khinds10/EnvironmentClock/display/displayCommands.png

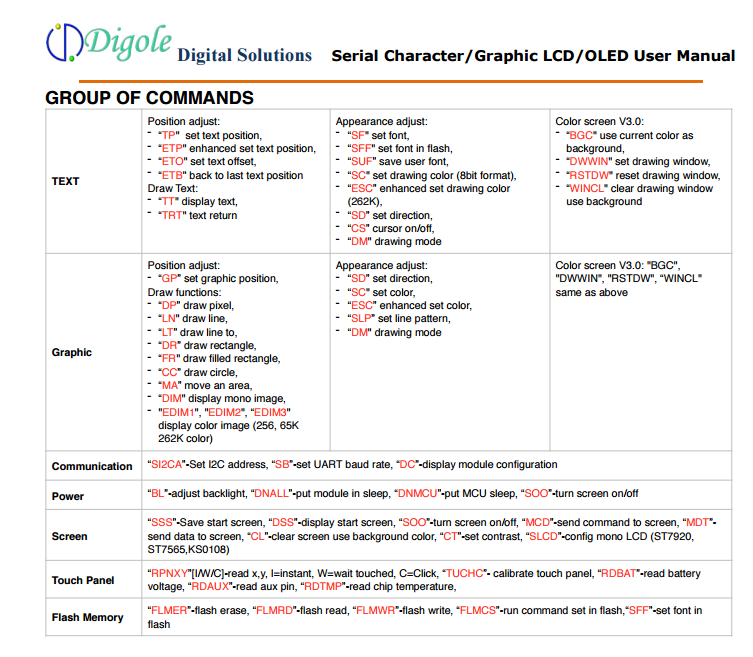
display/displayCommands.png
