khinds10/EnvironmentClock/display/build/images/cloudy.jpg

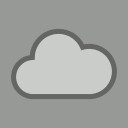
display/build/images/cloudy.jpg
