khinds10/EnvironmentClock/display/build/images/partly-cloudy-day.jpg

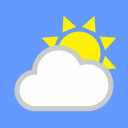
display/build/images/partly-cloudy-day.jpg
