khinds10/EnvironmentClock/display/build/images/rain.jpg

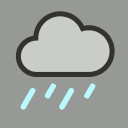
display/build/images/rain.jpg
