khinds10/EnvironmentClock/display/build/images/wind.jpg

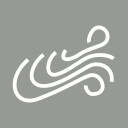
display/build/images/wind.jpg
